MichaelEischer/weather-display/display/components/GxEPD2/src/GxEPD2_426_GDEQ0426T82Mod.h

// Display Library for SPI e-paper panels from Dalian Good Display and boards from Waveshare.
// Requires HW SPI and Adafruit_GFX. Caution: the e-paper panels require 3.3V supply AND data lines!
//
// based on Demo Example from Good Display, available here: https://www.good-display.com/comp/xcompanyFile/downloadNew.do?appId=24&fid=1722&id=1158
// Panel: GDEQ0426T82 : https://www.good-display.com/product/457.html
// Controller : SSD1677 : https://v4.cecdn.yun300.cn/100001_1909185148/SSD1677.pdf
//
// Author: Jean-Marc Zingg
//
// Version: see library.properties
//
// Library: https://github.com/ZinggJM/GxEPD2

#ifndef _GxEPD2_426_GDEQ0426T82Mod_H_
#define _GxEPD2_426_GDEQ0426T82Mod_H_

#include "../code/src/GxEPD2_EPD.h"

class GxEPD2_426_GDEQ0426T82Mod : public GxEPD2_EPD
{
  public:
    // attributes
    static const uint16_t WIDTH = 800; // source, max 960
    static const uint16_t WIDTH_VISIBLE = WIDTH;
    static const uint16_t HEIGHT = 480; // gates, max 680
    static const GxEPD2::Panel panel = GxEPD2::GDEQ0426T82;
    static const bool hasColor = false;
    static const bool hasPartialUpdate = true;
    static const bool hasFastPartialUpdate = false;
    static const bool useFastFullUpdate = true; // set false for extended (low) temperature range
    static const uint16_t power_on_time = 100; // ms, e.g. 83873us
    static const uint16_t power_off_time = 200; // ms, e.g. 138810us
    static const uint16_t full_refresh_time = 1600; // ms, e.g. 1567341us
    static const uint16_t partial_refresh_time = 600; // ms, e.g. 499962us
    // constructor
    GxEPD2_426_GDEQ0426T82Mod(int16_t cs, int16_t dc, int16_t rst, int16_t busy);
    // methods (virtual)
    //  Support for Bitmaps (Sprites) to Controller Buffer and to Screen
    void clearScreen(uint8_t value = 0xFF); // init controller memory and screen (default white)
    void writeScreenBuffer(uint8_t value = 0xFF); // init controller memory (default white)
    // write to controller memory, without screen refresh; x and w should be multiple of 8
    void writeImage(const uint8_t bitmap[], int16_t x, int16_t y, int16_t w, int16_t h, bool invert = false, bool mirror_y = false, bool pgm = false);
    void writeImagePart(const uint8_t bitmap[], int16_t x_part, int16_t y_part, int16_t w_bitmap, int16_t h_bitmap,
                        int16_t x, int16_t y, int16_t w, int16_t h, bool invert = false, bool mirror_y = false, bool pgm = false);
    void refresh(bool partial_update_mode = false); // screen refresh from controller memory to full screen
    void refresh(int16_t x, int16_t y, int16_t w, int16_t h); // screen refresh from controller memory, partial screen
    void powerOff(); // turns off generation of panel driving voltages, avoids screen fading over time
    void hibernate(); // turns powerOff() and sets controller to deep sleep for minimum power use, ONLY if wakeable by RST (rst >= 0)
  private:
    void _writeScreenBuffer(uint8_t command, uint8_t value);
    void _writeImage(uint8_t command, const uint8_t bitmap[], int16_t x, int16_t y, int16_t w, int16_t h, bool invert = false, bool mirror_y = false, bool pgm = false);
    void _writeImagePart(uint8_t command, const uint8_t bitmap[], int16_t x_part, int16_t y_part, int16_t w_bitmap, int16_t h_bitmap,
                         int16_t x, int16_t y, int16_t w, int16_t h, bool invert = false, bool mirror_y = false, bool pgm = false);
    void _setPartialRamArea(uint16_t x, uint16_t y, uint16_t w, uint16_t h);
    void _InitDisplay();
    void _Update_Full();
    void _Update_Part();
};

#endif
